simoninns/lenovo-legion-go-controller-connector/images/2.jpg

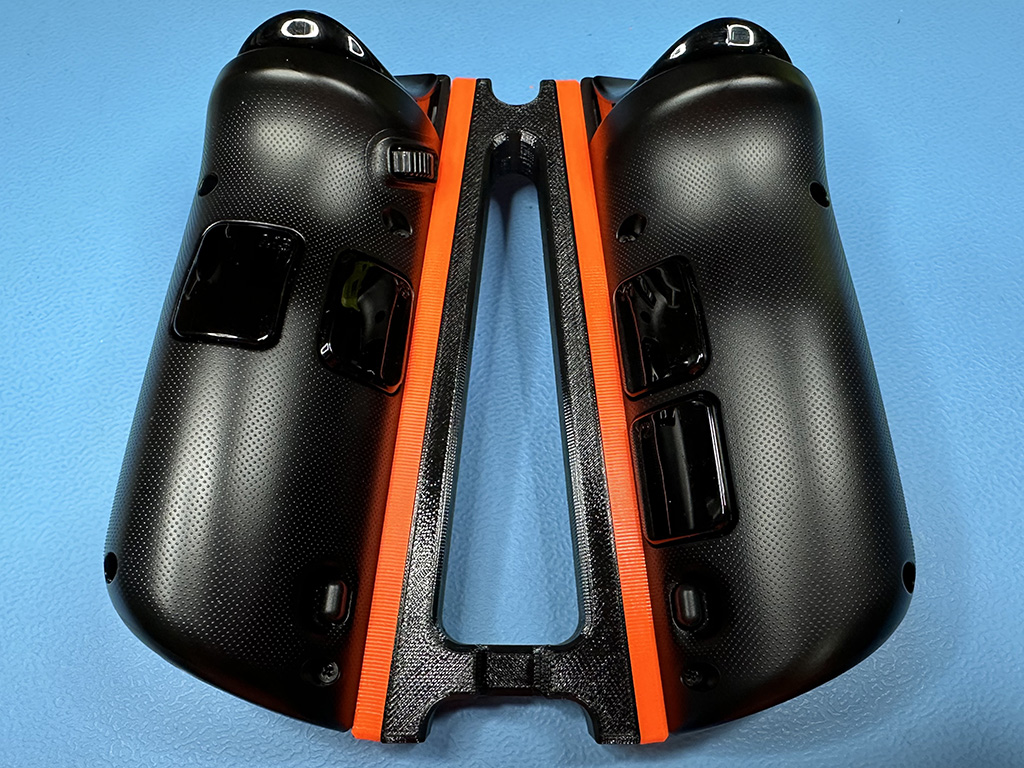
images/2.jpg
